8BitMixtape/ESPTINY86_MixtapePCB/images/ESPTINY86_3d_view__v02.png

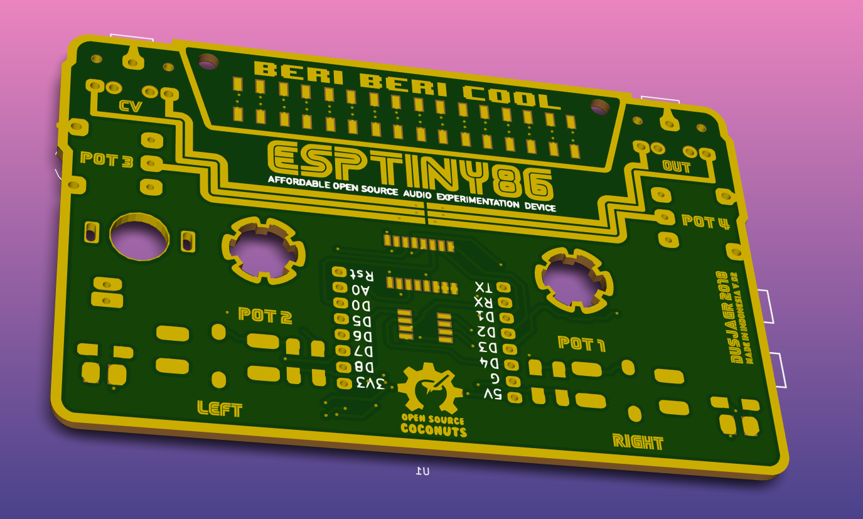
images/ESPTINY86_3d_view__v02.png
